brad112358/easy_E22/images/tin_pads.jpg

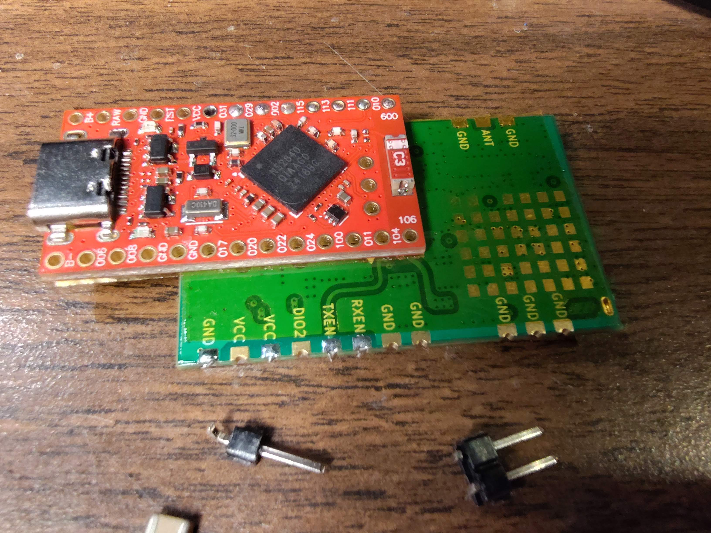
images/tin_pads.jpg
